simoninns/LiberPlayer/Documentation/Design/LiberPlayer Architecture PNG/Slide5.PNG

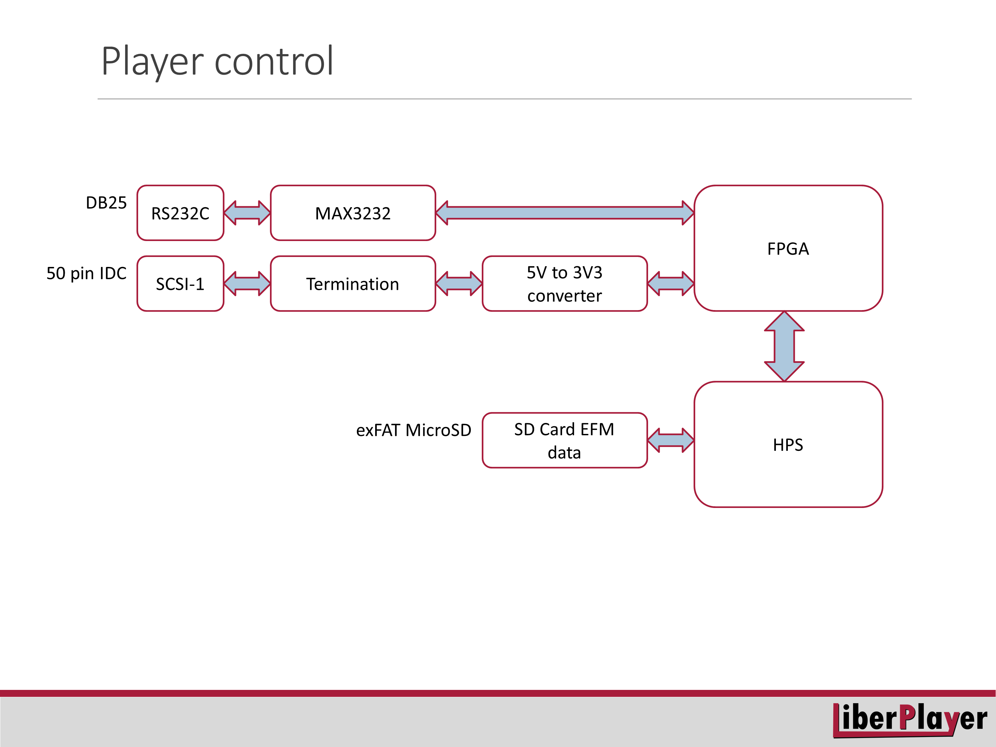
Documentation/Design/LiberPlayer Architecture PNG/Slide5.PNG
