simoninns/LiberPlayer/Documentation/Design/LiberPlayer Architecture PNG/Slide6.PNG

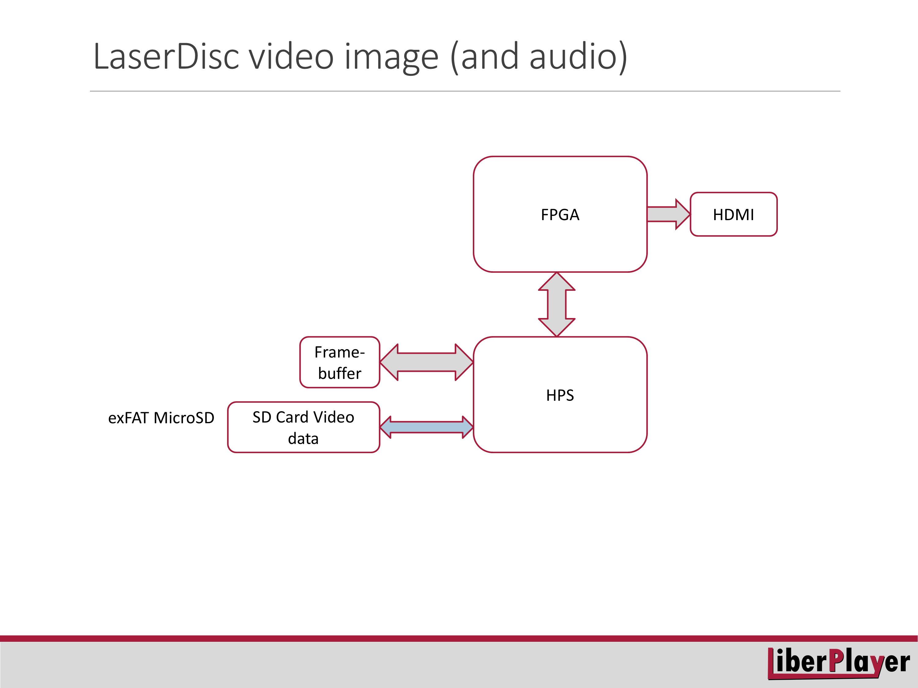
Documentation/Design/LiberPlayer Architecture PNG/Slide6.PNG
